donovinlewis/CloudGarden/Hardware Design/2.0/PXL_20201116_215413213 (1).jpg

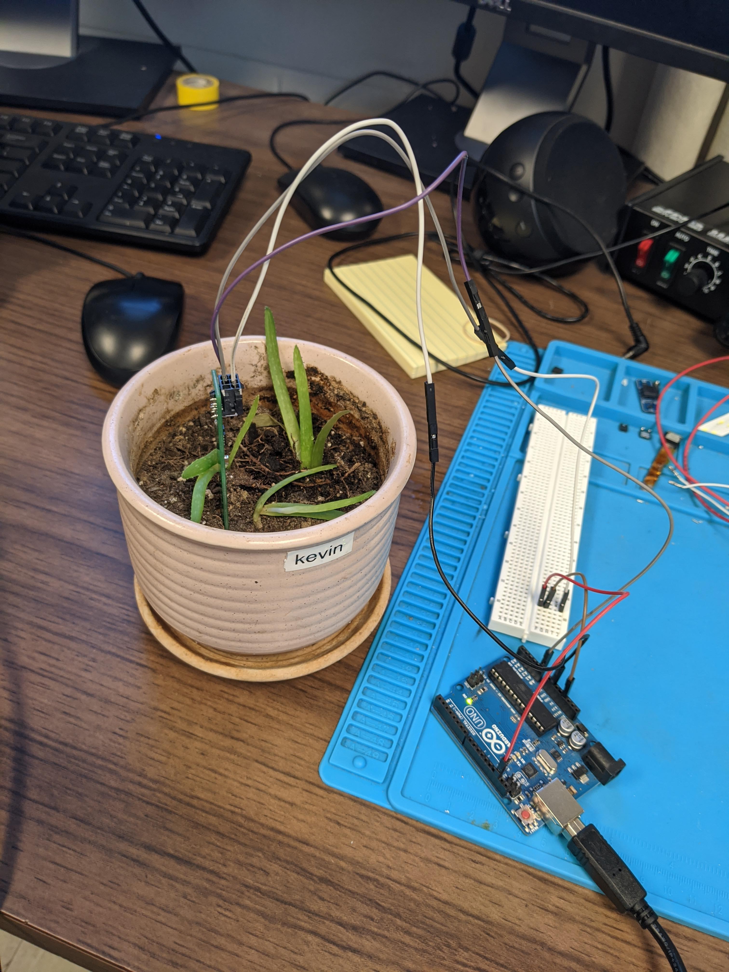
Hardware Design/2.0/PXL_20201116_215413213 (1).jpg
