donovinlewis/CloudGarden/Integration Testing/Microcontroller Testing/Blink_Test/Blink_Test.ino

/*
  Blink
  Turns on an LED on for one second, then off for one second, repeatedly.

  This example code is in the public domain.
 */

#define LEDP PD4

// the setup routine runs once when you press reset:
void setup() {
  // initialize the digital pin as an output.
  pinMode(LEDP, OUTPUT);
}

// the loop routine runs over and over again forever:
void loop() {
  digitalWrite(LEDP, HIGH);// turn the LED on (HIGH is the voltage level)
  delay(500);
  digitalWrite(LEDP,LOW);
  delay(1000);
}
